Spo-ck/Air-Quality-Aerosol-VOC-Sensor-and-Alarm/Photos/IMG_7284.jpg

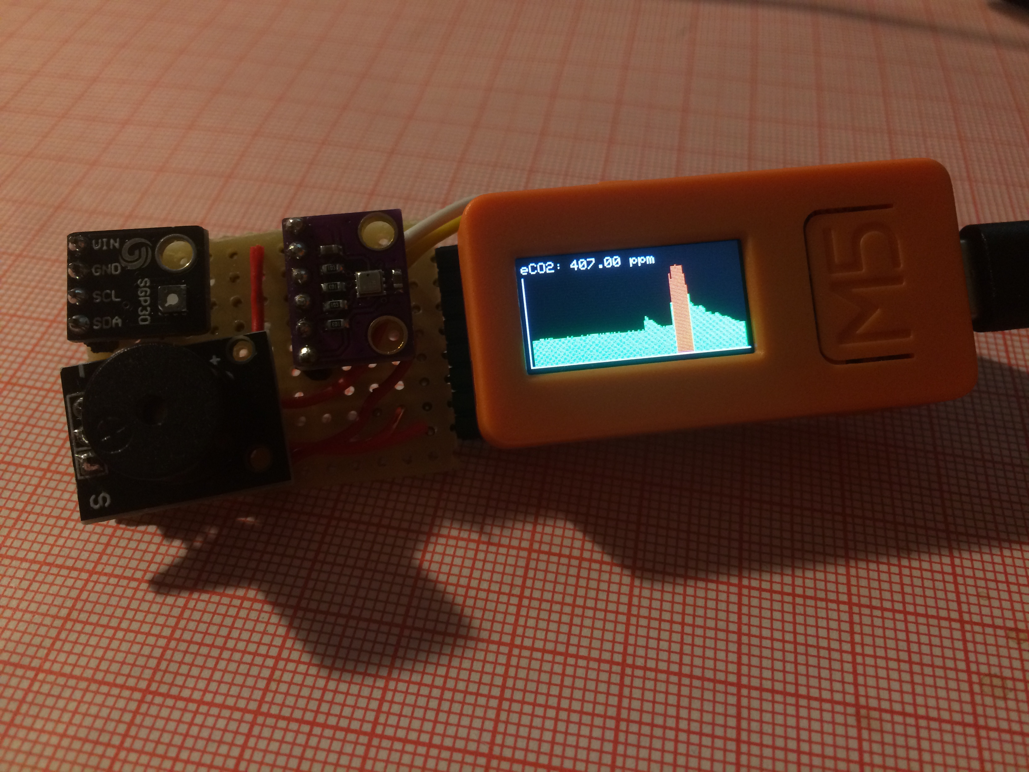
Photos/IMG_7284.jpg
