Spo-ck/Air-Quality-Aerosol-VOC-Sensor-and-Alarm/Photos/IMG_7303.jpg

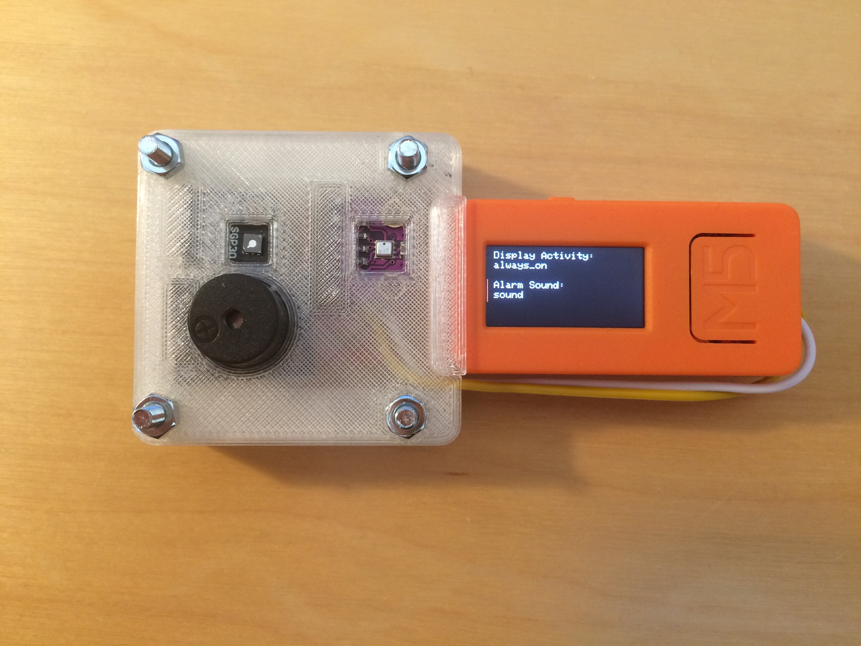
Photos/IMG_7303.jpg
